vymaztom/Temperature-controller-with-ESP8266/Image/console.png

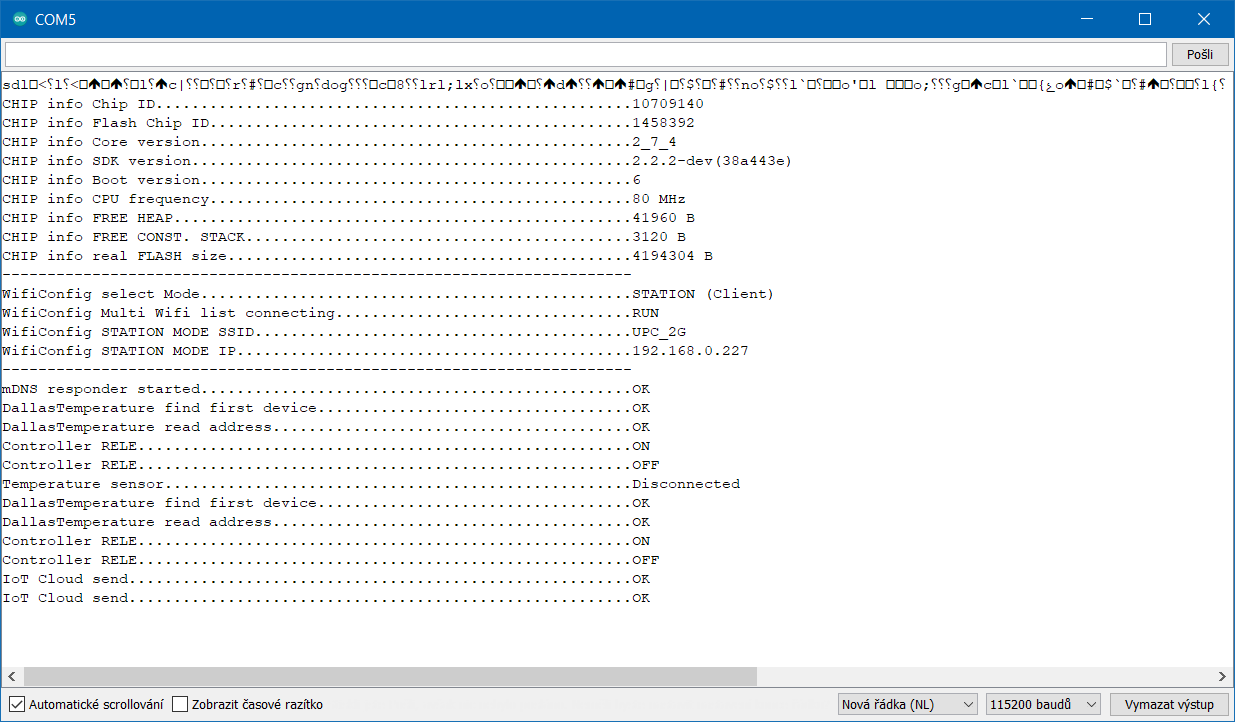
Image/console.png
