vymaztom/Temperature-controller-with-ESP8266/Image/fron_view.png

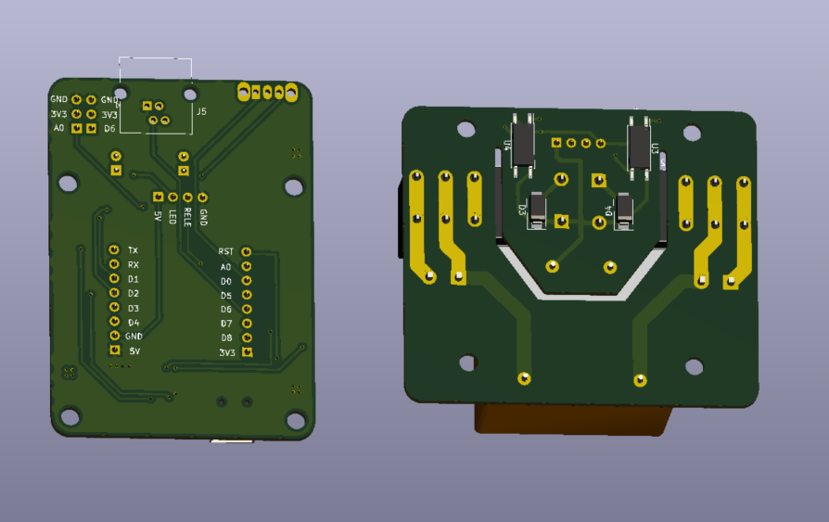
Image/fron_view.png
