vymaztom/Temperature-controller-with-ESP8266/Image/mapačidel.png

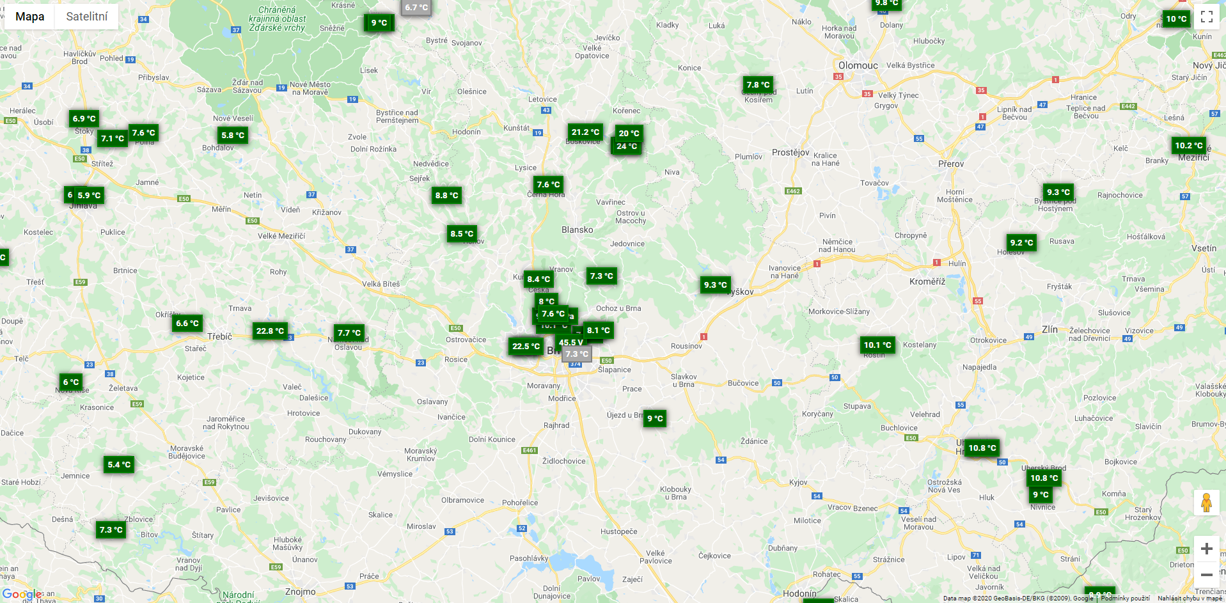
Image/mapačidel.png
