vymaztom/Temperature-controller-with-ESP8266/Image/periferie_rele.png

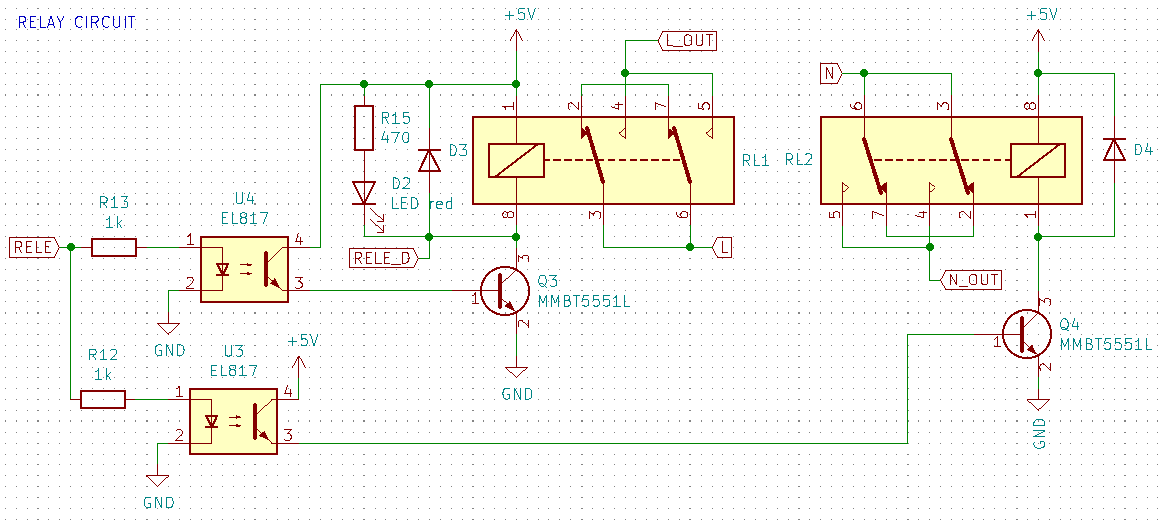
Image/periferie_rele.png
