vymaztom/Temperature-controller-with-ESP8266/Image/PIC009.JPG

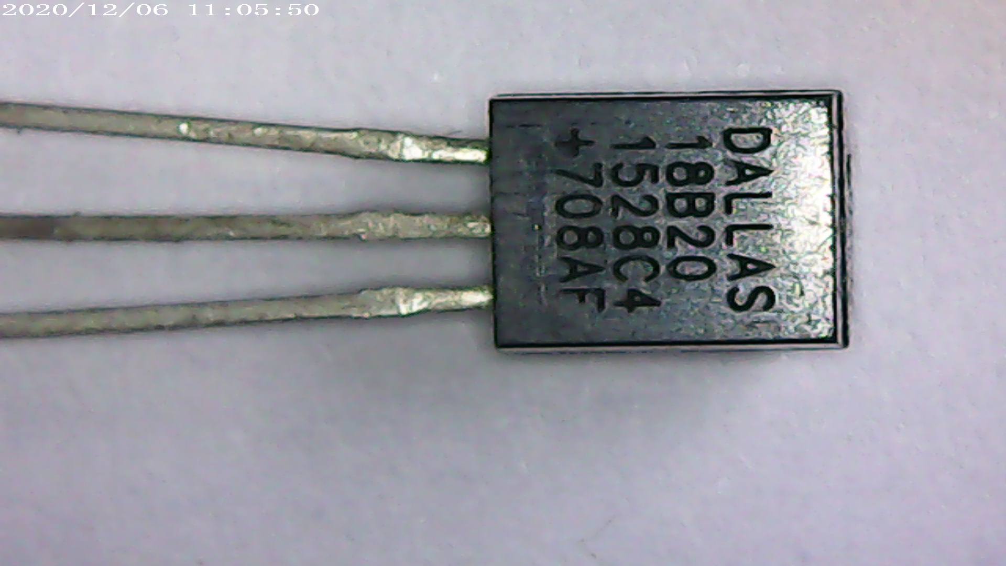
Image/PIC009.JPG
