vymaztom/Temperature-controller-with-ESP8266/Image/PIC015.JPG

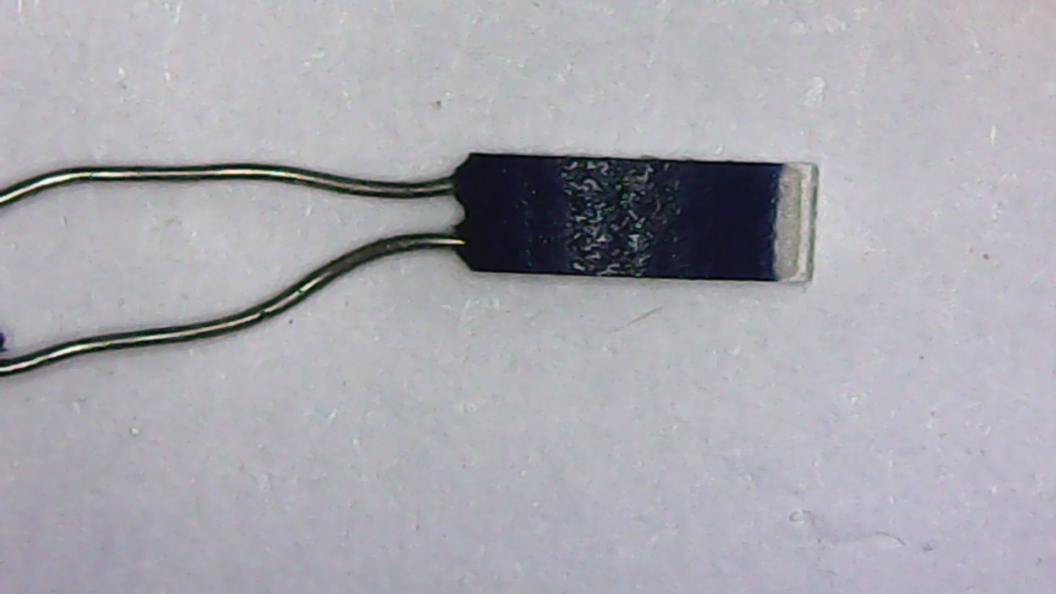
Image/PIC015.JPG
