vymaztom/Temperature-controller-with-ESP8266/Image/voltcraft203_4.bmp

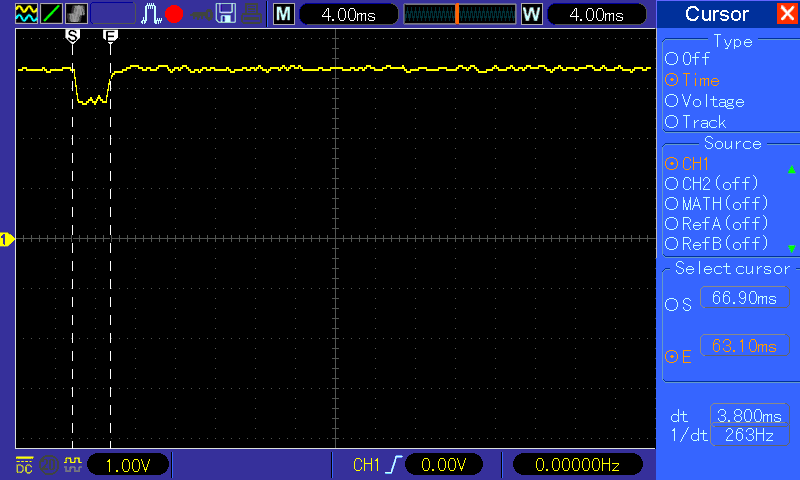
Image/voltcraft203_4.bmp
