vymaztom/Temperature-controller-with-ESP8266/Image/web_config stránka.png

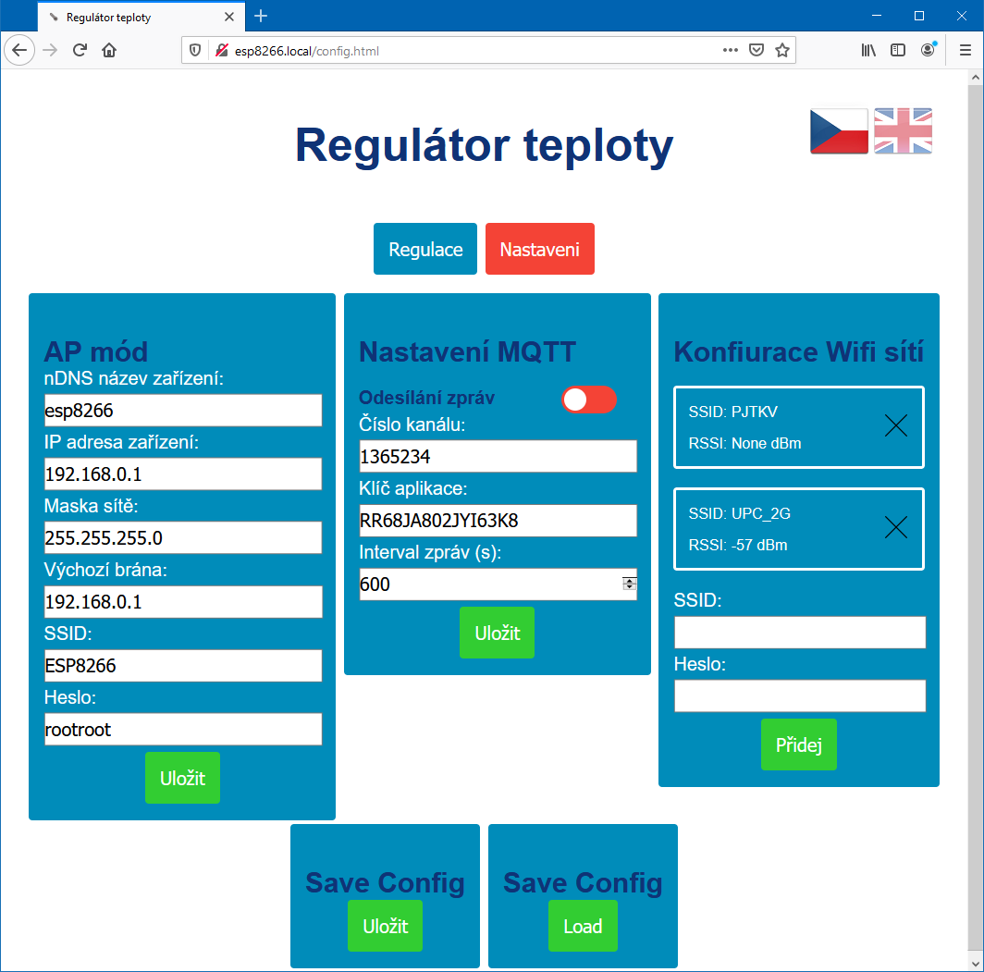
Image/web_config stránka.png
