vymaztom/Temperature-controller-with-ESP8266/Image/web_úodní stránka.png

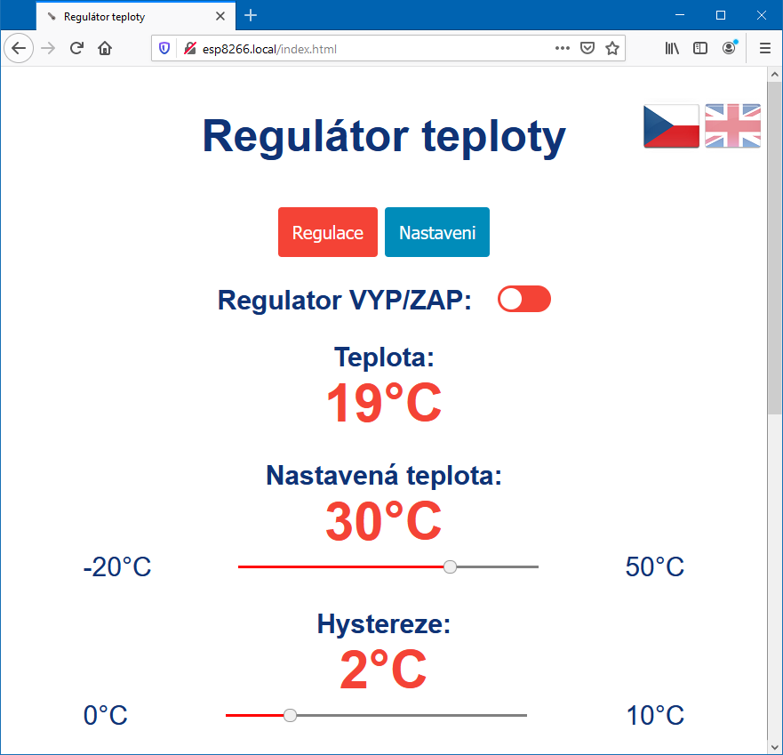
Image/web_úodní stránka.png
