vymaztom/Temperature-controller-with-ESP8266/Image/zdrojová deska.png

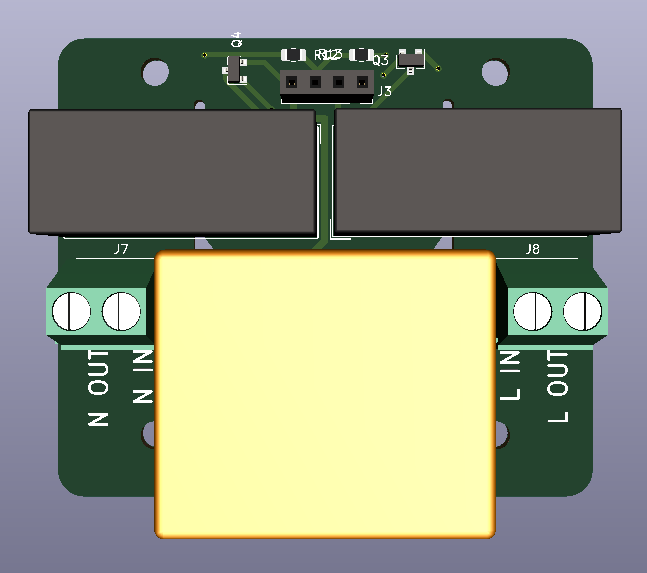
Image/zdrojová deska.png
