vymaztom/Temperature-controller-with-ESP8266/Osciloskop_OBR/voltcraft203_5/voltcraft203_5.bmp

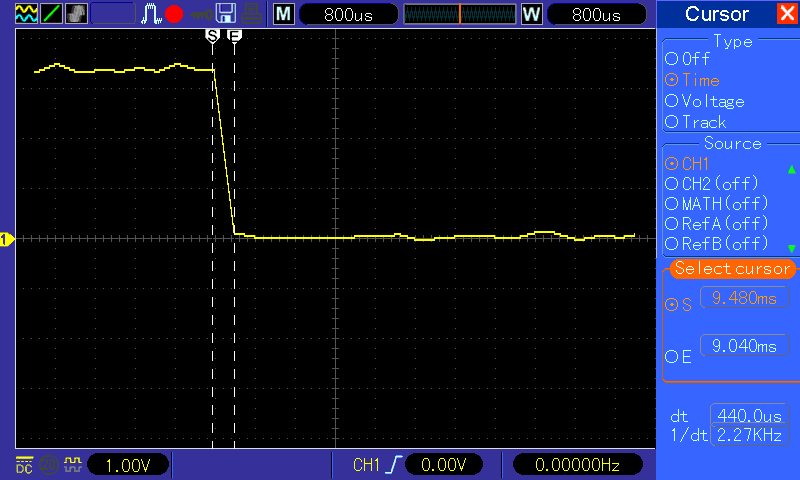
Osciloskop_OBR/voltcraft203_5/voltcraft203_5.bmp
