vymaztom/Temperature-controller-with-ESP8266/Osciloskop_OBR/voltcraft203_9/voltcraft203_9.bmp

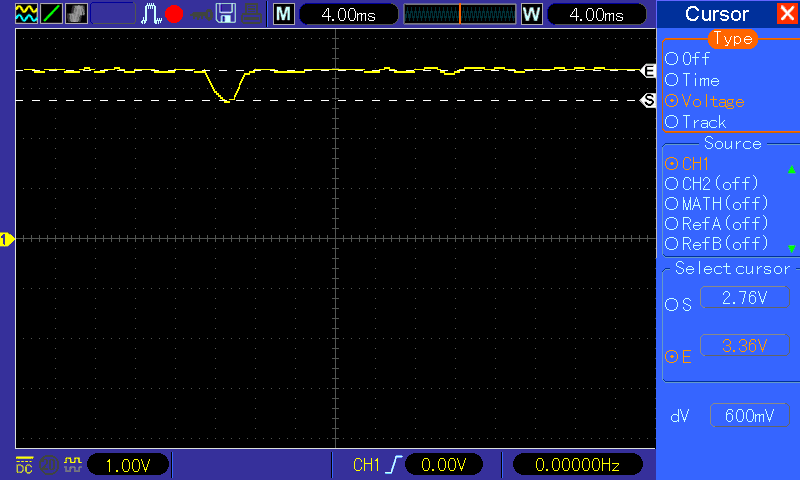
Osciloskop_OBR/voltcraft203_9/voltcraft203_9.bmp
