vymaztom/Temperature-controller-with-ESP8266/PS digram/main.png

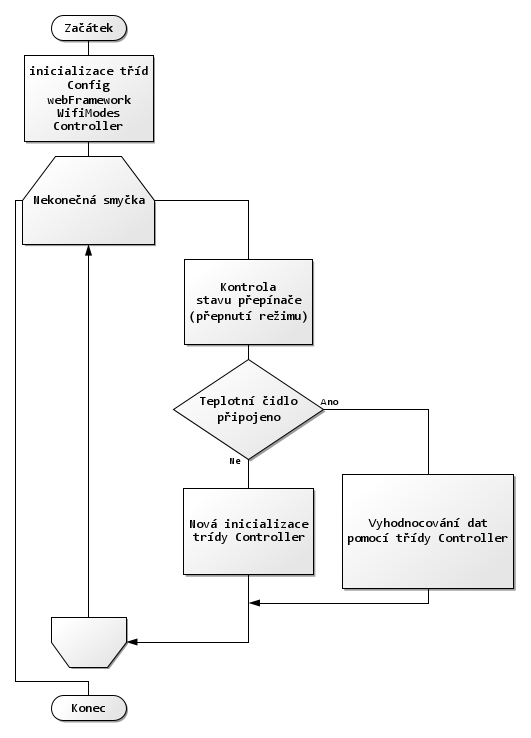
PS digram/main.png
