vymaztom/Temperature-controller-with-ESP8266/RECORD/PIC000.JPG

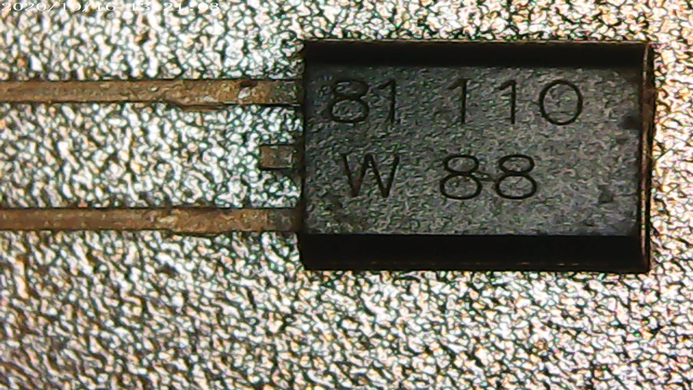
RECORD/PIC000.JPG
