vymaztom/Temperature-controller-with-ESP8266/RECORD/PIC001.JPG

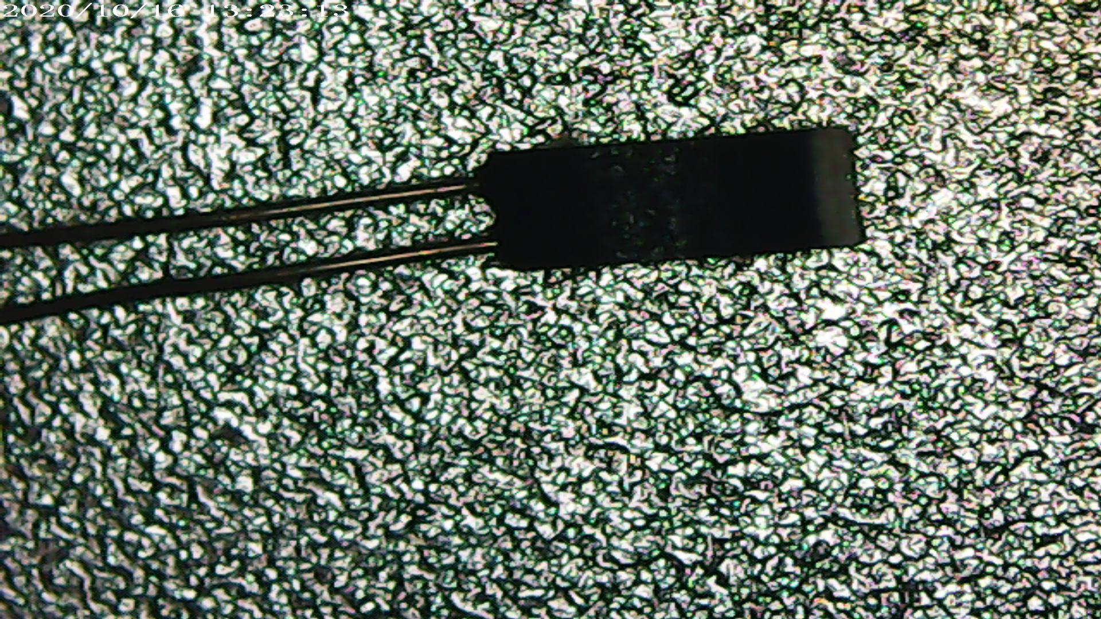
RECORD/PIC001.JPG
