vymaztom/Temperature-controller-with-ESP8266/RECORD/PIC002.JPG

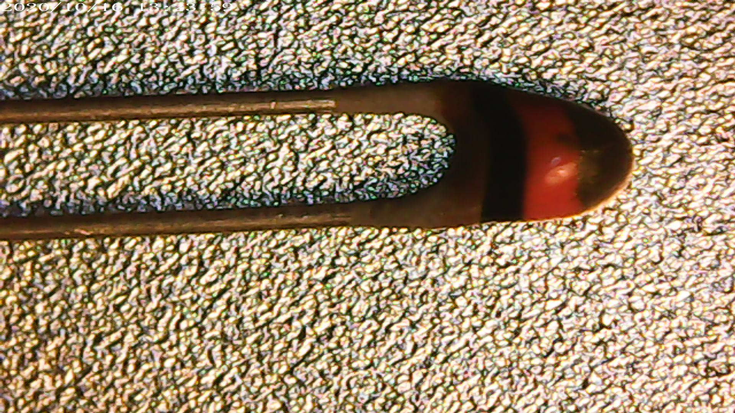
RECORD/PIC002.JPG
