vymaztom/Temperature-controller-with-ESP8266/RECORD/PIC003.JPG

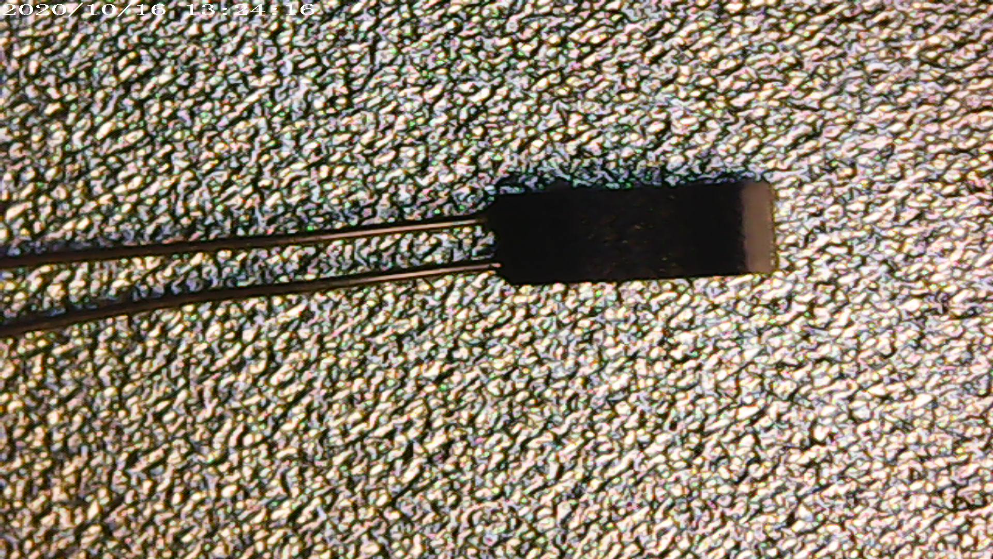
RECORD/PIC003.JPG
