vymaztom/Temperature-controller-with-ESP8266/RECORD/PIC004.JPG

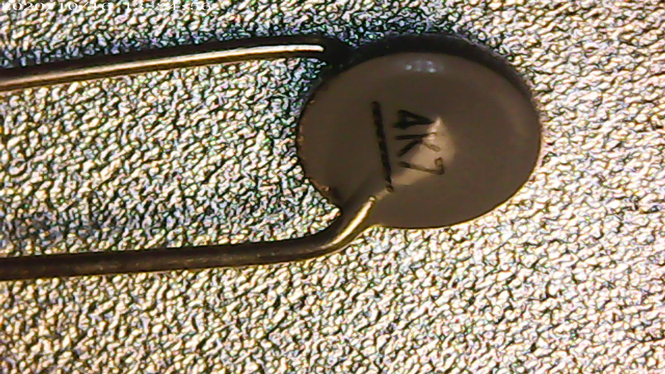
RECORD/PIC004.JPG
