vymaztom/Temperature-controller-with-ESP8266/RECORD/PIC005.JPG

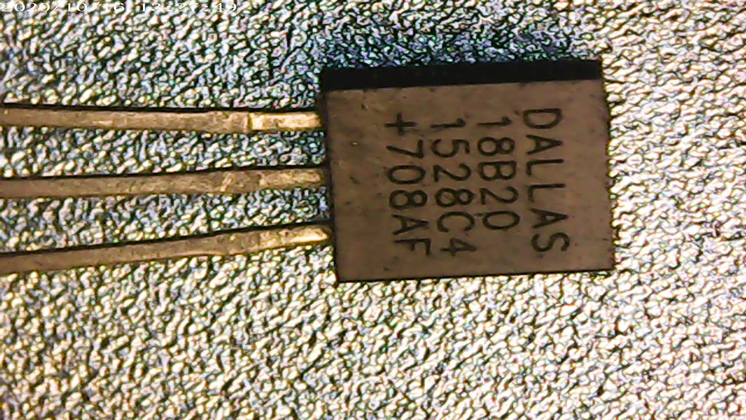
RECORD/PIC005.JPG
