vymaztom/Temperature-controller-with-ESP8266/RECORD/PIC006.JPG

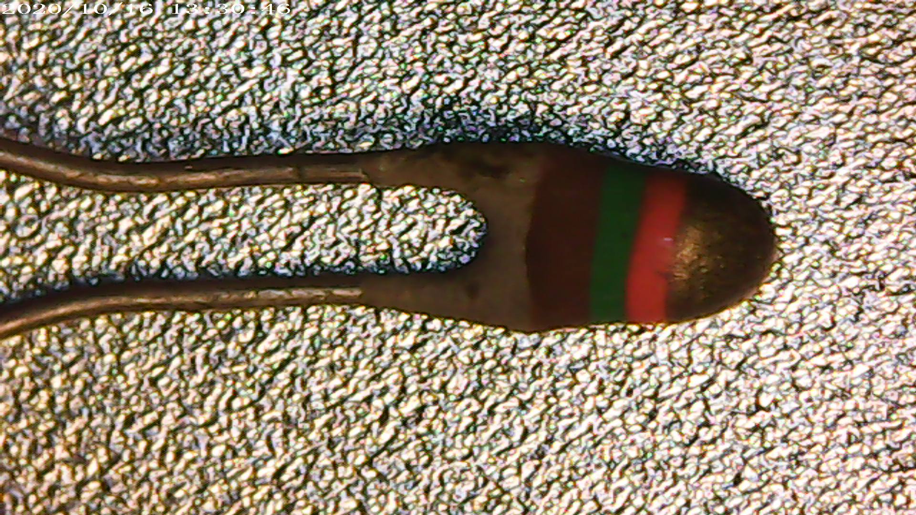
RECORD/PIC006.JPG
