vymaztom/Temperature-controller-with-ESP8266/RECORD/PIC007.JPG

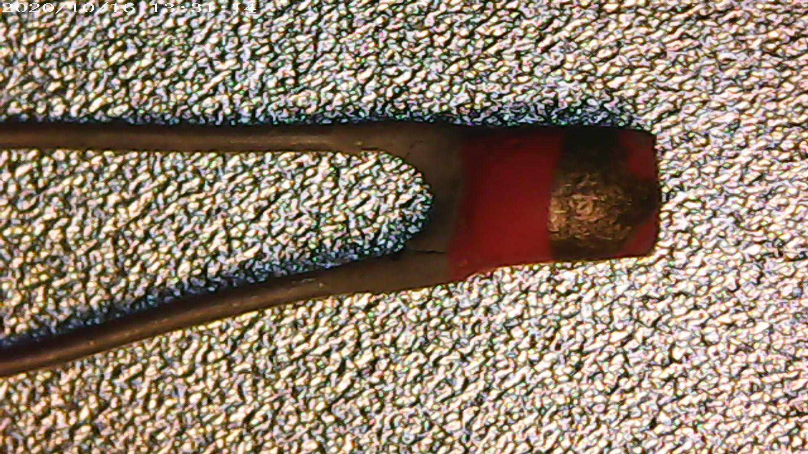
RECORD/PIC007.JPG
