vymaztom/Temperature-controller-with-ESP8266/RECORD/PIC008.JPG

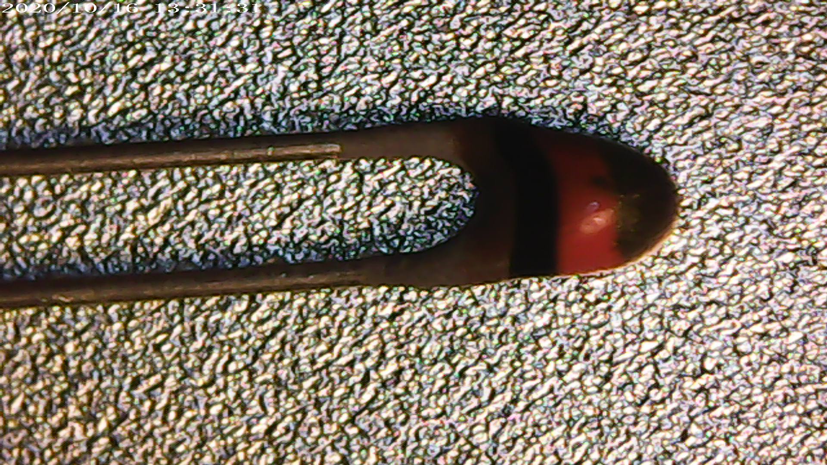
RECORD/PIC008.JPG
