vymaztom/Temperature-controller-with-ESP8266/code/TWI_test/TWI_test.ino

#include <Wire.h>

#define PIN_SCL 5
#define PIN_SDA 4

byte error, address;
int nDevices;

void setup() {

	Wire.begin(PIN_SDA, PIN_SCL);
	Serial.begin(115200);


}



/******************************************************************************

									LOOP

******************************************************************************/



void loop(){
	Serial.println("Scanning...");

	nDevices = 0;
	for(address = 1; address < 127; address++ ){

		Wire.beginTransmission(address);
		error = Wire.endTransmission();

		if (error == 0){
			Serial.print("I2C device found at address 0x");
			if (address<16)
			Serial.print("0");
			Serial.print(address,HEX);
			Serial.println("  !");

			nDevices++;
		}
		else if (error==4){
			Serial.print("Unknow error at address 0x");
			if (address<16)
			Serial.print("0");
			Serial.println(address,HEX);
		}
	}
	if (nDevices == 0) Serial.println("No I2C devices found\n");
	else Serial.println("done\n");

	delay(5000);           // wait 5 seconds for next scan
}
